adamgann/dsn-art/images/source/lro.png

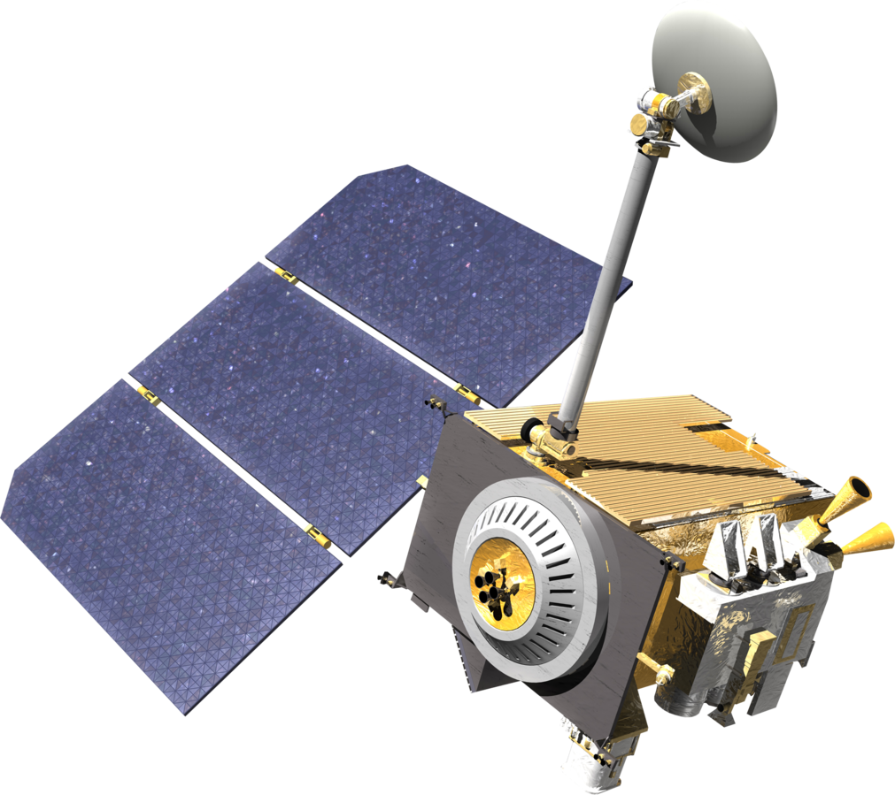
images/source/lro.png
