adamgann/dsn-art/images/source/lucy.png

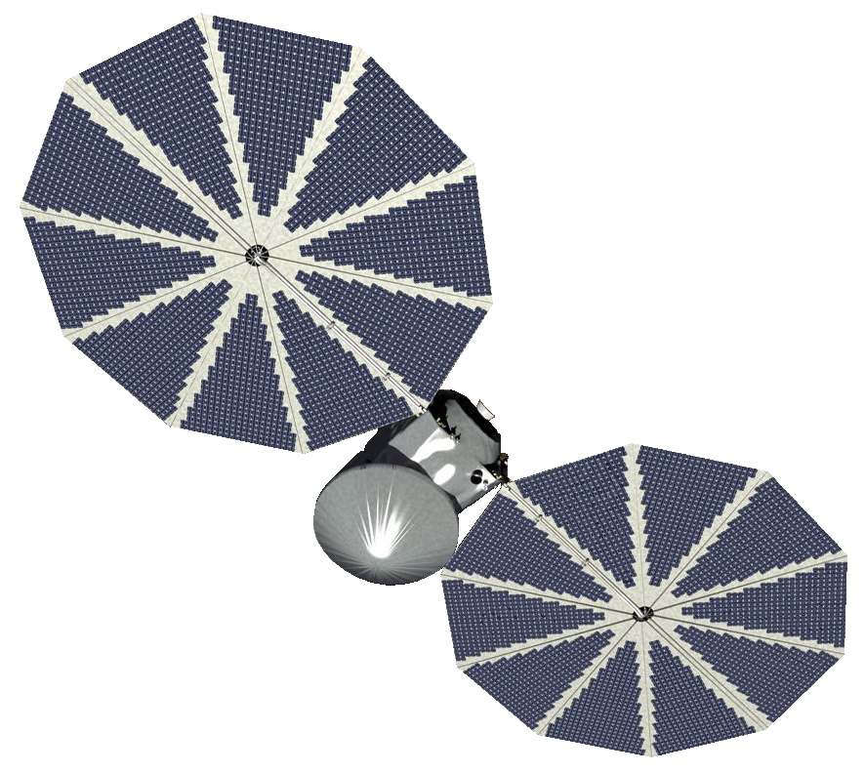
images/source/lucy.png
