adamgann/dsn-art/images/source/percy.png

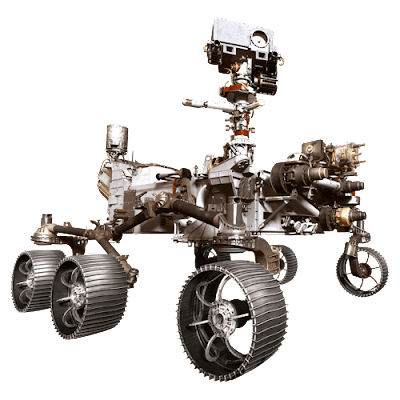
images/source/percy.png
